jbulikk/Gesture-Glove/Software/Core/Inc/electrodes.h

#ifndef ELECTRODES_H_
#define ELECTRODES_H_

#endif /* ELECTRODES_H_ */
#include <stdint.h>

typedef struct 
{
    volatile uint8_t thumb;  
    volatile uint8_t index;
    volatile uint8_t middle;
} Electrodes;
